BoujeeEnjinia1701/heliolite/cad/drawings/HLT-DWG-001.pdf

CONCEPT, NOT FOR FABRICATION | HelioLite · github.com/BoujeeEnjinia1701/heliolite

FRONT VIEW
Scale 1:25; looking at the front (along +Y)

TOP VIEW
Scale 1:25; looking down (along -Z)

RIGHT VIEW
Scale 1:25; looking at the right side (along -X)

928

934

2,200 axis

2265

1,712 mast top

600 mirror
680 arms c/c

1,100 box base

550

ISOMETRIC VIEW, TRACKING POSE
Not to scale; seen from the front right and above, about 30 deg elevation

MAIN DIMENSIONS AND INTERFACES (MM)
Mirror 600 x 600 x 3 glass on 4 ACP, EPDM edge channel; sweep radius 301 Elevation axis at Z 2,200; 25 sq. torque tube, 14 trunnions
Yoke: 40 x 60 x 2 alu. tube arms at X +/-340; gaps 20 (arm), 56 (crossbar) Drives: NEMA17 on NMRV030-class 50:1, envelope 80 x 97 x 63, 14 bore Mast 60.3 x 3.9 galv. pipe, 1,700 long; floor flange; cap 160 sq. x 8 Anchor flange 220 dia.; ground screw 76 x 800 (not shown)
Anemometer at Z 1,500, reach 550; controller box at Z 1,100
Stow lug 8 thk at X -307; pad and pawl at R 55 on a 6 alu. bracket, -X arm
Preload spring cans 50 dia.: -X trunnion and mast top
Top mass about 12.99 kg, fitted in two lifts; stow face-down in 23 s (HLT-CAL-001) Orthographic views stowed at azimuth 0; front from -Y, right from +X
REV | DESCRIPTION | DATE | BY
P1 | Preliminary GA for TRL 3 (from cad/src/model.py) | 2026-09-25 | AC
P2 | Stow stop and latch, preload springs added (DDR-002) | 2026-09-25 | AC
P3 | Layout and labels tidied | 2026-09-25 | AC
P4 | Design for construction (DDR-003): tube yoke, fixings | 2026-10-01 | AC
P5 | Decisions of 2026-10-02: alu. latch bracket, EPDM edge channel | 2026-10-02 | AC
HELIOLITE | github.com/BoujeeEnjinia1701/heliolite

## General arrangement

DRAWING NO.
HLT-DWG-001

REV
P5

SHEET
1 of 1

SIZE

## ANSI B

SCALE
1:25

UNITS
mm
PROJECTION | DATE
2026-10-02

DRAWN
Amish Chadha

MATERIAL / NOTES
Glass mirror on ACP; aluminum tube yoke; NMRV030-class drives; 60.3 mm galv. pipe. PRELIMINARY, NOT FOR FABRICATION
Licensed CERN-OHL-S-2.0 · Design Molecule Lab · designmolecule.com | Generated from cad/src; do not edit by hand
