BoujeeEnjinia1701/heliolite/cad/drawings/HLT-DWG-104.pdf

### BUILD PLAN SKETCH, PLAN NOT YET BUILT HelioLite · github.com/BoujeeEnjinia1701/heliolite

FRONT VIEW
Scale 1:1; looking at the front (along +Y)

TOP VIEW
Scale 1:1; looking down (along -Z)

RIGHT VIEW
Scale 1:1; looking at the right side (along -X)

8

94 38

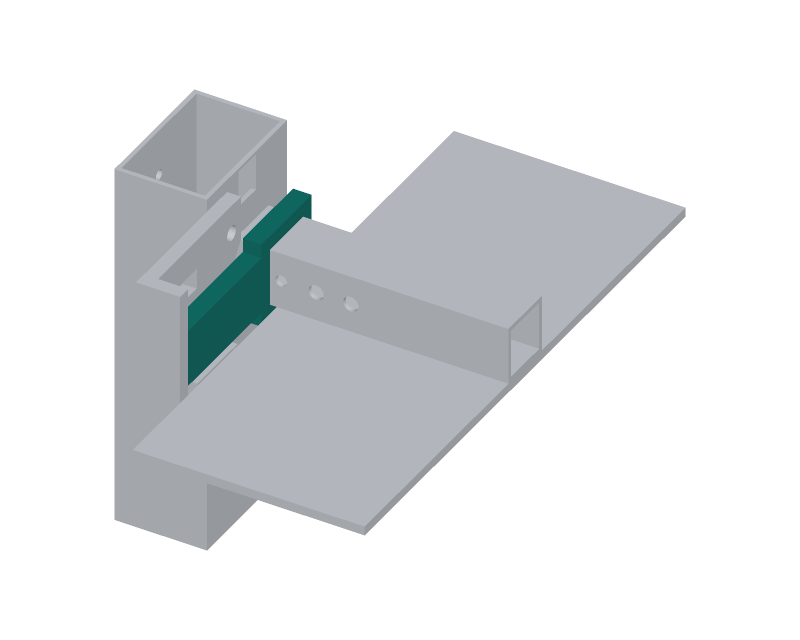
[picture p6: figure]

WHERE IT GOES
This part in colour, its neighbours in grey

HOW TO MAKE IT AND HOW IT FITS
Cut from 8 mm steel plate: a collar 37.5 mm square with a
tongue 25 mm wide running out to 75 mm from the collar's centre. Cut the 25 mm square hole in the collar: drill 20 mm, file square to a sliding fit on the torque tube.
Drill and tap M5 through the collar side opposite the tongue
for a set screw.
On one face of the tongue, 30 mm from the centre: a 6 mm hole 3 mm deep for the homing magnet (glue it in).
Round the tongue corners 2 mm and break all edges.
Fit: slides onto the left end of the torque tube, magnet toward the arm, mid-plane 11 mm from the tube end; set screw into the spot on the tube, medium threadlocker.
When stowed, the tongue rests on the stop pad and the latch pawl closes over it.
Check: the tongue is square to the tube and does not rock.
REV | DESCRIPTION | DATE | BY
P1 | Making sketch for the prototype build plan | 2026-10-02 | AC
HELIOLITE | github.com/BoujeeEnjinia1701/heliolite

## HelioLite stow lug: making sketch

DRAWING NO.
HLT-DWG-104

REV
P1

SHEET
1 of 1

SIZE

## ANSI B

SCALE
1:1

UNITS
mm
PROJECTION | DATE
2026-10-02

DRAWN
Amish Chadha

MATERIAL / NOTES
Steel plate 8 mm, S275 or similar, painted
Licensed CERN-OHL-S-2.0 · Design Molecule Lab · designmolecule.com | Generated from cad/src; do not edit by hand
