BoujeeEnjinia1701/heliolite/cad/drawings/HLT-DWG-107.pdf

### BUILD PLAN SKETCH, PLAN NOT YET BUILT HelioLite · github.com/BoujeeEnjinia1701/heliolite

FRONT VIEW
Scale 1:5; looking at the front (along +Y)

TOP VIEW
Scale 1:5; looking down (along -Z)

RIGHT VIEW
Scale 1:5; looking at the right side (along -X)

40

60 397

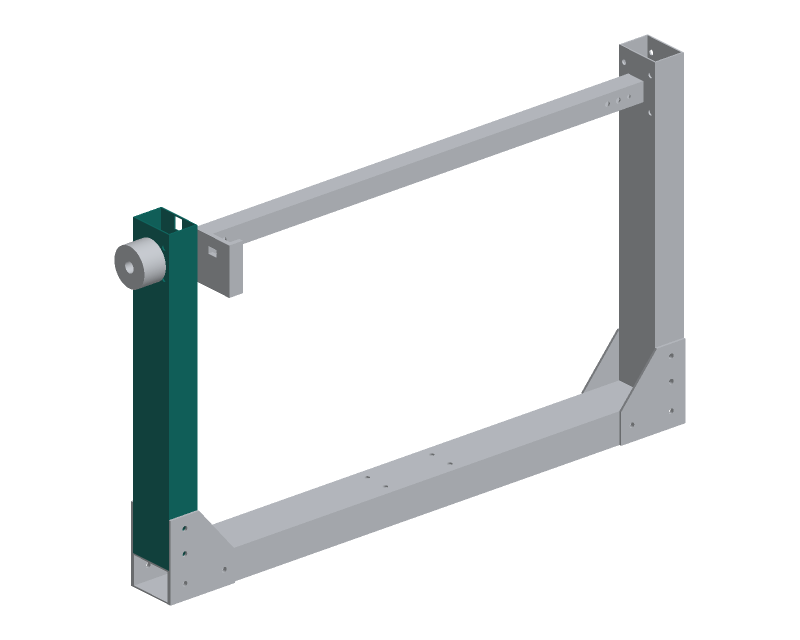
[picture p7: figure]

WHERE IT GOES
This part in colour, its neighbours in grey

HOW TO MAKE IT AND HOW IT FITS
Cut and drill as the right arm (HLT-DWG-106) for length, bush hole and gusset bolt holes, but without the four gearbox holes.
Spring can holes: three 4.5 mm on a 40 mm circle round the bush hole, outer side only.
Latch bracket holes: two 6.5 mm through both sides, 8 mm from the front face, 18 mm and 55 mm below the top end.
Hall switch window: 13 mm wide and 16 mm tall through the inner side only, 1.5 mm below the top end, centred across the side. Fit: as the right arm; the latch bracket bolts to the inner side
at the front, the spring can to the outer side.
Check: lay both arms side by side: bush holes and gusset holes match.
REV | DESCRIPTION | DATE | BY
P1 | Making sketch for the prototype build plan | 2026-10-02 | AC
HELIOLITE | github.com/BoujeeEnjinia1701/heliolite

## HelioLite left arm (latch side): making sketch

DRAWING NO.
HLT-DWG-107

REV
P1

SHEET
1 of 1

SIZE

## ANSI B

SCALE
1:5

UNITS
mm
PROJECTION | DATE
2026-10-02

DRAWN
Amish Chadha

MATERIAL / NOTES
Aluminum rectangular tube 60 x 40 x 2 mm, 6063
Licensed CERN-OHL-S-2.0 · Design Molecule Lab · designmolecule.com | Generated from cad/src; do not edit by hand
