BoujeeEnjinia1701/heliolite/cad/drawings/HLT-DWG-110.pdf

### BUILD PLAN SKETCH, PLAN NOT YET BUILT HelioLite · github.com/BoujeeEnjinia1701/heliolite

FRONT VIEW
Scale 1:1; looking at the front (along +Y)

TOP VIEW
Scale 1:1; looking down (along -Z)

RIGHT VIEW
Scale 1:1; looking at the right side (along -X)

27

68 62

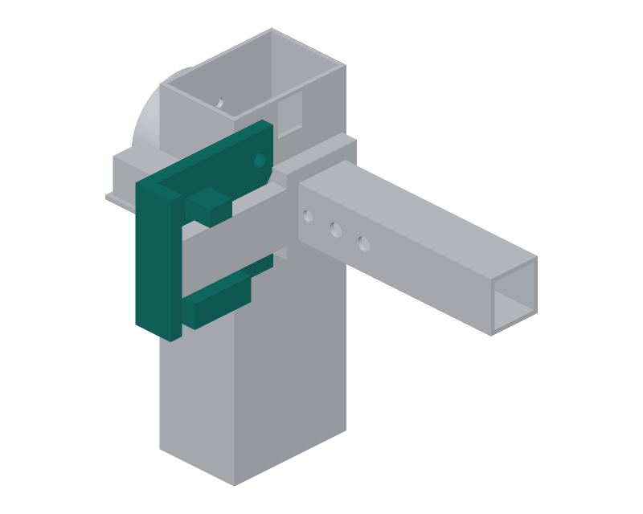
[picture p8: figure]

WHERE IT GOES
This part in colour, its neighbours in grey

HOW TO MAKE IT AND HOW IT FITS
Bracket: cut 62 mm of 6 mm aluminum angle with legs of at least 70 and 20 mm. Trim the long leg to 68 mm and the short leg to 19 mm overall (13 mm clear of the long leg). No bending.
In the long leg: a 21 mm radius bite at the back edge, centred
31 mm up, clear of the turning tube end; a 14 x 9 mm slot for
the pawl, 21 mm from the front edge, 40 mm up. Two 6.6 mm countersunk holes 7 mm from the back edge, 12.5 and 49.5 mm up. Stop block: 13 x 30 x 11.5 mm aluminum bar, screwed to the leg's foot with two M5 screws; bond the 3 mm polyurethane pad on top. Pawl: 26 mm of 12 x 8 mm steel bar; chamfer the top of its tip
45 degrees by 4 mm; tap M3 in the tail for the solenoid plunger. Fit: long leg flat on the left arm's inner side, two M6
countersunk screws; the pawl slides in the slot over the lug. Check: the pawl slides freely 12 mm; pad top 0.5 mm under the stowed lug.
REV | DESCRIPTION | DATE | BY
P1 | Making sketch for the prototype build plan | 2026-10-02 | AC
HELIOLITE | github.com/BoujeeEnjinia1701/heliolite

## HelioLite latch bracket, stop block and pawl: making sketch

DRAWING NO.
HLT-DWG-110

REV
P1

SHEET
1 of 1

SIZE

## ANSI B

SCALE
1:1

UNITS
mm
PROJECTION | DATE
2026-10-02

DRAWN
Amish Chadha

MATERIAL / NOTES
Aluminum angle 6 mm and bar 15 x 30 mm, 6063-T6; steel bar 12 x 8 mm (pawl)
Licensed CERN-OHL-S-2.0 · Design Molecule Lab · designmolecule.com | Generated from cad/src; do not edit by hand
