BoujeeEnjinia1701/heliolite/cad/drawings/HLT-DWG-114.pdf

### BUILD PLAN SKETCH, PLAN NOT YET BUILT HelioLite · github.com/BoujeeEnjinia1701/heliolite

FRONT VIEW
Scale 1:1; looking at the front (along +Y)

TOP VIEW
Scale 1:1; looking down (along -Z)

RIGHT VIEW
Scale 1:1; looking at the right side (along -X)

30

50 50

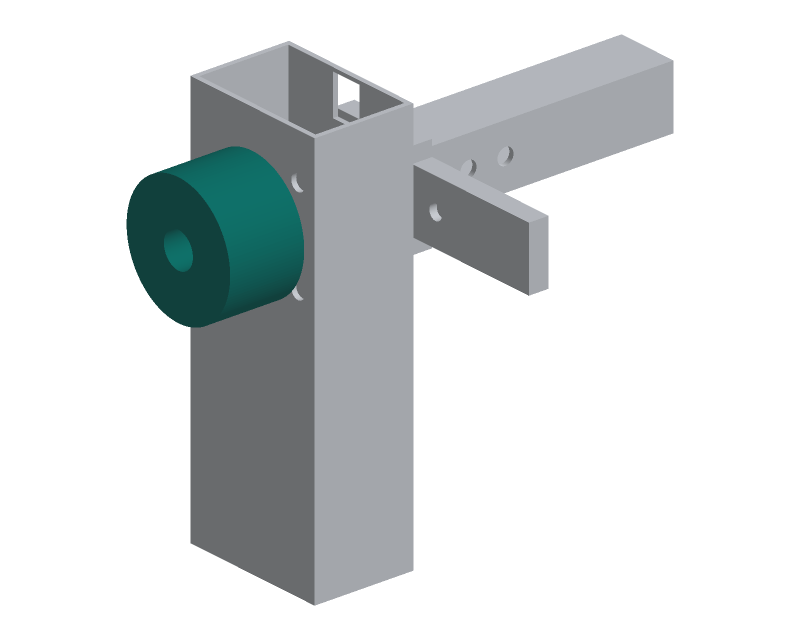
[picture p9: figure]

WHERE IT GOES
This part in colour, its neighbours in grey

HOW TO MAKE IT AND HOW IT FITS
Elevation can: a 50 mm diameter cup 30 mm long with a 14 mm centre hole through its closed end, the open end toward the arm. Three 4.5 mm holes on a 40 mm circle, lengthwise, for M4 screws into the left arm and plug. A 3 mm pin hole near the rim inside holds the spring's outer end.
Azimuth can: the same cup at 52.5 mm diameter, a push fit in the mast pipe, with an M5 insert in its side for a screw through
the pipe wall, 37 mm below the pipe's top end.
Fit the bought flat spiral spring: inner end in the stub's slot
(or the shaft's), outer end on the pin. Wind it 1 turn before fixing so it holds about 3 N m toward stow.
Check: the spring holds the shaft one way with no slack.
REV | DESCRIPTION | DATE | BY
P1 | Making sketch for the prototype build plan | 2026-10-02 | AC
HELIOLITE | github.com/BoujeeEnjinia1701/heliolite

## HelioLite spring can (make 2, printed): making sketch

DRAWING NO.
HLT-DWG-114

REV
P1

SHEET
1 of 1

SIZE

## ANSI B

SCALE
1:1

UNITS
mm
PROJECTION | DATE
2026-10-02

DRAWN
Amish Chadha

MATERIAL / NOTES
ASA, printed; 100 % infill
Licensed CERN-OHL-S-2.0 · Design Molecule Lab · designmolecule.com | Generated from cad/src; do not edit by hand
