BoujeeEnjinia1701/heliolite/cad/drawings/HLT-DWG-101.pdf

### BUILD PLAN SKETCH, PLAN NOT YET BUILT HelioLite · github.com/BoujeeEnjinia1701/heliolite

FRONT VIEW
Scale 1:5; looking at the front (along +Y)

TOP VIEW
Scale 1:5; looking down (along -Z)

RIGHT VIEW
Scale 1:5; looking at the right side (along -X)

25

560 40

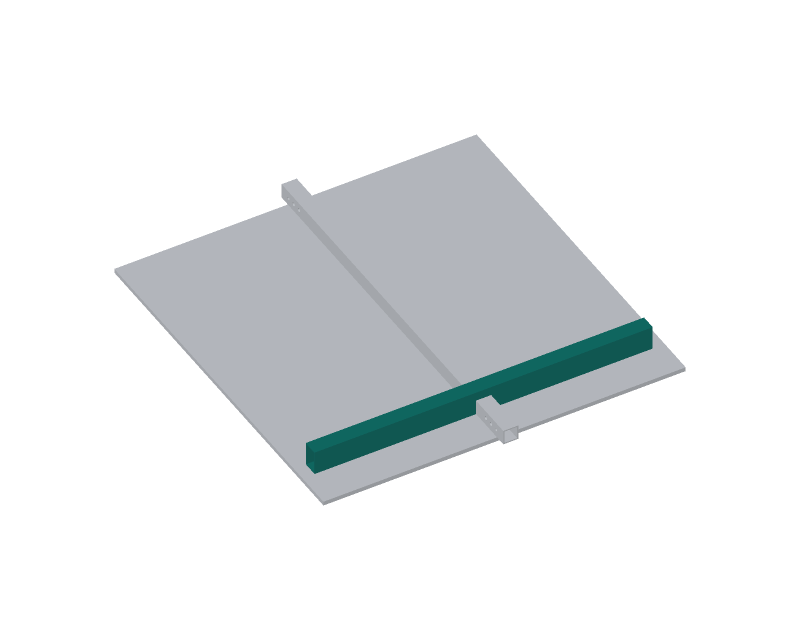
[picture p52: figure]

WHERE IT GOES
This part in colour, its neighbours in grey

HOW TO MAKE IT AND HOW IT FITS
Cut two 560 mm lengths of 25 x 40 x 1.5 mm tube; square and deburr. Tunnel for the torque tube, at mid-length (280 mm from each end):
a notch 25.5 mm long and 25.25 mm deep, cut from one 25 mm face (the face that goes on the panel) down through both 40 mm sides. Saw the two sides, chain drill and file the floor flat.
Push a 25 mm tube offcut through the tunnel: it must slide, not rock. Fit plastic end caps in both ends.
Fit: the notched face is bonded to the back of the backing panel with structural silicone, the rib centre line 227.5 mm from the panel centre line and its ends 20 mm in from the panel edges.
The torque tube runs through both tunnels and touches the panel. Check: both tunnels line up when the ribs lie side by side.
REV | DESCRIPTION | DATE | BY
P1 | Making sketch for the prototype build plan | 2026-10-01 | AC
HELIOLITE | github.com/BoujeeEnjinia1701/heliolite

## HelioLite rib tube (make 2): making sketch

DRAWING NO.
HLT-DWG-101

REV
P1

SHEET
1 of 1

SIZE

## ANSI B

SCALE
1:5

UNITS
mm
PROJECTION | DATE
2026-10-01

DRAWN
Amish Chadha

MATERIAL / NOTES
Aluminum rectangular tube 25 x 40 x 1.5 mm, 6063
Licensed CERN-OHL-S-2.0 · Design Molecule Lab · designmolecule.com | Generated from cad/src; do not edit by hand
