BoujeeEnjinia1701/heliolite/cad/drawings/HLT-DWG-102.pdf

### BUILD PLAN SKETCH, PLAN NOT YET BUILT HelioLite · github.com/BoujeeEnjinia1701/heliolite

FRONT VIEW
Scale 1:5; looking at the front (along +Y)

TOP VIEW
Scale 1:5; looking down (along -Z)

RIGHT VIEW
Scale 1:5; looking at the right side (along -X)

636

25 25

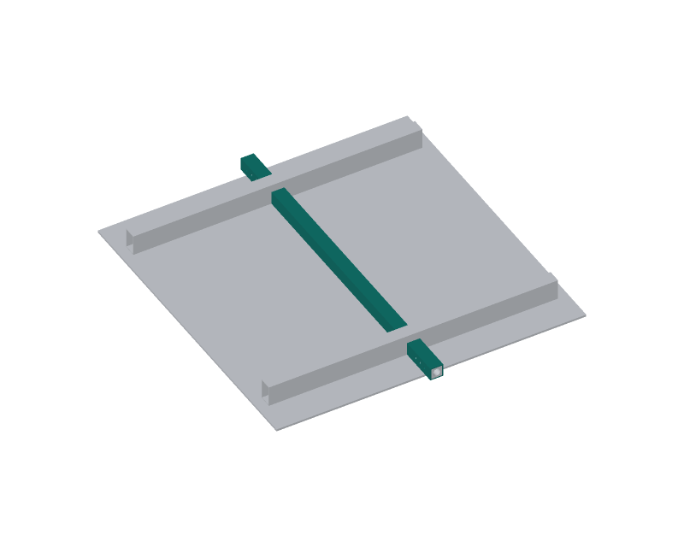
[picture p53: figure]

WHERE IT GOES
This part in colour, its neighbours in grey

HOW TO MAKE IT AND HOW IT FITS
Cut to 635 mm (1 mm shorter than the 636 mm between the bush flanges, so the mirror drops into the yoke). Square both ends.
Through both side walls, 6.5 mm holes 35 and 50 mm from each end (end block bolts), on the centre line of the side.
Through both side walls, a 5 mm hole 20 mm from each end (cross pin): drill these with the end blocks and stubs in place (step 11).
On the left end only: a shallow 4 mm spot 11 mm from the end on
the face away from the panel, for the stow lug's set screw.
Deburr inside and out so the end blocks slide in.
Fit: runs through both rib tunnels, its top face bonded to the panel with structural silicone; ends 318 mm each side of the centre. Check: straight within 0.5 mm over its length on a flat bench.
REV | DESCRIPTION | DATE | BY
P1 | Making sketch for the prototype build plan | 2026-10-01 | AC
HELIOLITE | github.com/BoujeeEnjinia1701/heliolite

## HelioLite torque tube: making sketch

DRAWING NO.
HLT-DWG-102

REV
P1

SHEET
1 of 1

SIZE

## ANSI B

SCALE
1:5

UNITS
mm
PROJECTION | DATE
2026-10-01

DRAWN
Amish Chadha

MATERIAL / NOTES
Aluminum square tube 25 x 25 x 2 mm, 6063
Licensed CERN-OHL-S-2.0 · Design Molecule Lab · designmolecule.com | Generated from cad/src; do not edit by hand
