BoujeeEnjinia1701/heliolite/cad/drawings/HLT-DWG-103.pdf

### BUILD PLAN SKETCH, PLAN NOT YET BUILT HelioLite · github.com/BoujeeEnjinia1701/heliolite

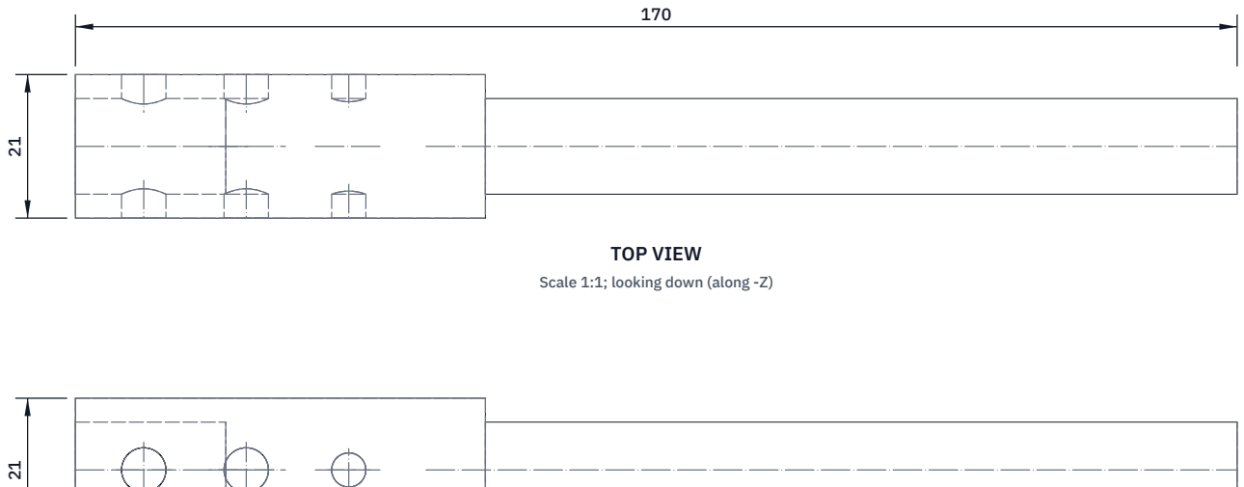
[picture p54: figure]
TOP VIEW; Scale 1:1; looking down (along -Z)

FRONT VIEW
Scale 1:1; looking at the front (along +Y)

RIGHT VIEW
Scale 1:1; looking at the right side (along -X)

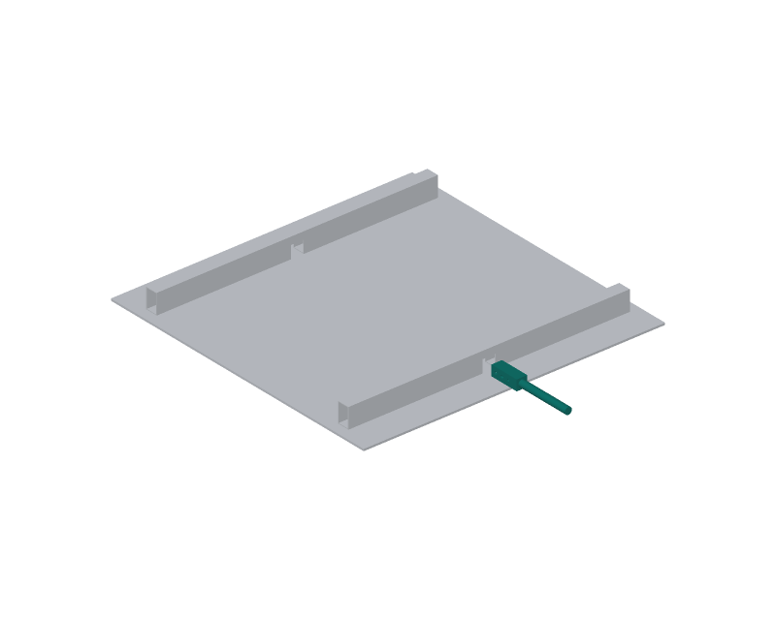
[picture p55: figure]

WHERE IT GOES
This part in colour, its neighbours in grey

HOW TO MAKE IT AND HOW IT FITS
End blocks (make 2): cut 60 mm of 22 mm square bar; file to 21 mm square, a sliding fit in the tube. Drill and ream 14 mm along
the centre, right through. Cross holes 6.5 mm at 10 and 25 mm from the inner end, through two opposite faces.
Stubs: cut 14 mm keyed shaft (5 mm key) to 148 mm for the drive (right) side and 108 mm for the spring (left) side.
Each stub goes 38 mm into its block. With the stub in the block in the tube, drill 5 mm through tube, block and stub 20 mm from the tube end and drive in a 5 x 24 mm roll pin (step 11).
Left stub only: saw a 3 mm slot 10 mm deep across its outer end for the inner end of the spiral spring.
Fit: block bolted in the tube end with two M6 bolts; stub through the bronze bush, into the gearbox bore (right) or spring can (left). Check: the stub turns the tube with no play once pinned.
REV | DESCRIPTION | DATE | BY
P1 | Making sketch for the prototype build plan | 2026-10-01 | AC
HELIOLITE | github.com/BoujeeEnjinia1701/heliolite

## HelioLite trunnion end block and stub: making sketch

DRAWING NO.
HLT-DWG-103

REV
P1

SHEET
1 of 1

SIZE

## ANSI B

SCALE
1:1

UNITS
mm
PROJECTION | DATE
2026-10-01

DRAWN
Amish Chadha

MATERIAL / NOTES
Aluminum square bar 22 mm (block); 14 mm keyed steel shaft (stub)
Licensed CERN-OHL-S-2.0 · Design Molecule Lab · designmolecule.com | Generated from cad/src; do not edit by hand
