BoujeeEnjinia1701/heliolite/cad/drawings/HLT-DWG-105.pdf

### BUILD PLAN SKETCH, PLAN NOT YET BUILT HelioLite · github.com/BoujeeEnjinia1701/heliolite

FRONT VIEW
Scale 1:5; looking at the front (along +Y)

TOP VIEW
Scale 1:5; looking down (along -Z)

RIGHT VIEW
Scale 1:5; looking at the right side (along -X)

720

60 40

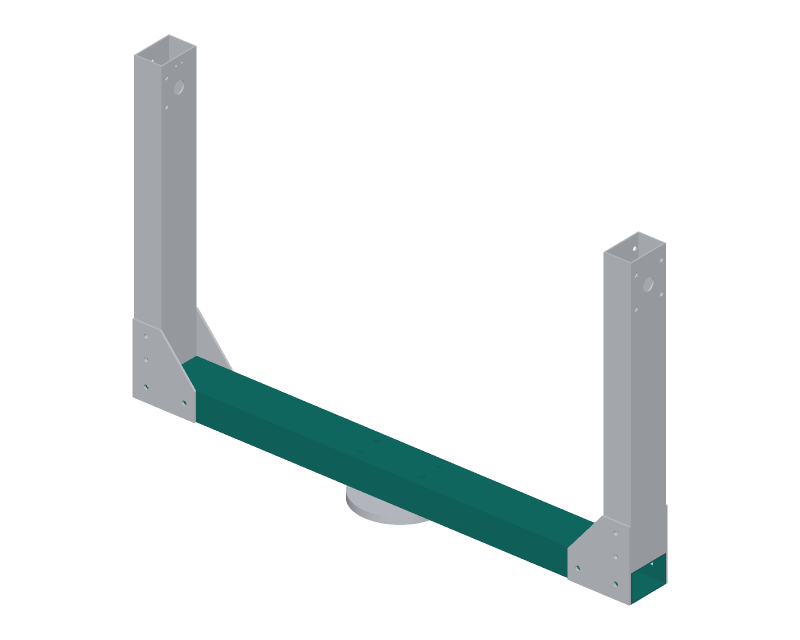
[picture p56: figure]

WHERE IT GOES
This part in colour, its neighbours in grey

HOW TO MAKE IT AND HOW IT FITS
Cut 720 mm of 60 x 40 x 2 mm tube; square and deburr the ends. Lay it with a 60 mm face up. All holes 6.5 mm.
Gusset bolt holes, horizontal through both 40 mm sides, at mid-height: 20 mm and 75 mm in from each end.
Turntable bolt holes, vertical through top and bottom: four holes, 45 mm each side of the centre and 15 mm each side of the centre line.
Slide a 6 mm bore aluminum crush sleeve into each bolt hole pair (cut to the inside height) so bolts do not crush the tube.
Fit: sits flat on the turntable disc, held by four M6 bolts into
the disc's tapped holes; the arms stand on its ends.
Check: holes in line; the tube lies flat on the disc.
REV | DESCRIPTION | DATE | BY
P1 | Making sketch for the prototype build plan | 2026-10-01 | AC
HELIOLITE | github.com/BoujeeEnjinia1701/heliolite

## HelioLite crossbar: making sketch

DRAWING NO.
HLT-DWG-105

REV
P1

SHEET
1 of 1

SIZE

## ANSI B

SCALE
1:5

UNITS
mm
PROJECTION | DATE
2026-10-01

DRAWN
Amish Chadha

MATERIAL / NOTES
Aluminum rectangular tube 60 x 40 x 2 mm, 6063
Licensed CERN-OHL-S-2.0 · Design Molecule Lab · designmolecule.com | Generated from cad/src; do not edit by hand
