BoujeeEnjinia1701/heliolite/cad/drawings/HLT-DWG-106.pdf

### BUILD PLAN SKETCH, PLAN NOT YET BUILT HelioLite · github.com/BoujeeEnjinia1701/heliolite

FRONT VIEW
Scale 1:5; looking at the front (along +Y)

TOP VIEW
Scale 1:5; looking down (along -Z)

RIGHT VIEW
Scale 1:5; looking at the right side (along -X)

40

60 397

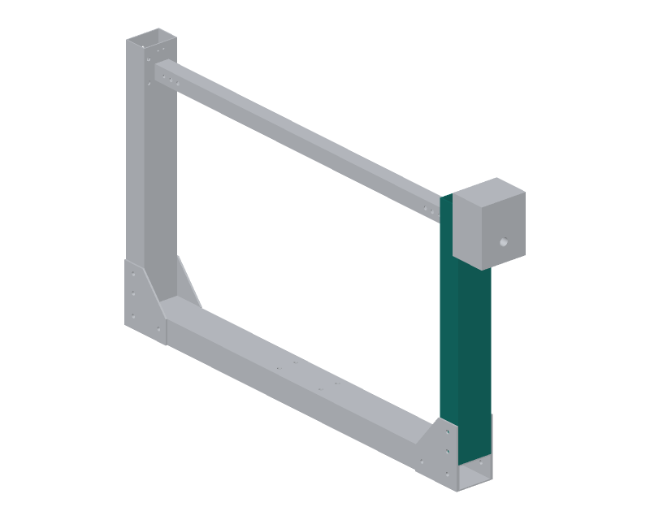
[picture p57: figure]

WHERE IT GOES
This part in colour, its neighbours in grey

HOW TO MAKE IT AND HOW IT FITS
Cut 397 mm of 60 x 40 x 2 mm tube; square and deburr. The 60 mm faces are the sides; the 40 mm faces are the front and back.
Bush hole: 18 mm through both sides, centred, 40 mm below the top end. Drill 6 mm pilot, open with a step drill, ream.
Gearbox holes (right arm): four 6.5 mm through both sides on a 44 mm square round the bush hole (22 mm each way). Check the gearbox's output-face holes before drilling.
Gusset bolt holes: 6.5 mm through the front and back faces, centred, 15 mm and 45 mm above the bottom end.
Fit: stands on the crossbar end; two gussets clamp it; the bearing plug fills its top 75 mm; the gearbox bolts to the
outer side.
Check: the bush hole is square to the side (a 14 mm rod through it stands at 90 degrees to the arm).
REV | DESCRIPTION | DATE | BY
P1 | Making sketch for the prototype build plan | 2026-10-01 | AC
HELIOLITE | github.com/BoujeeEnjinia1701/heliolite

## HelioLite right arm (drive side): making sketch

DRAWING NO.
HLT-DWG-106

REV
P1

SHEET
1 of 1

SIZE

## ANSI B

SCALE
1:5

UNITS
mm
PROJECTION | DATE
2026-10-01

DRAWN
Amish Chadha

MATERIAL / NOTES
Aluminum rectangular tube 60 x 40 x 2 mm, 6063
Licensed CERN-OHL-S-2.0 · Design Molecule Lab · designmolecule.com | Generated from cad/src; do not edit by hand
