BoujeeEnjinia1701/heliolite/cad/drawings/HLT-DWG-108.pdf

### BUILD PLAN SKETCH, PLAN NOT YET BUILT HelioLite · github.com/BoujeeEnjinia1701/heliolite

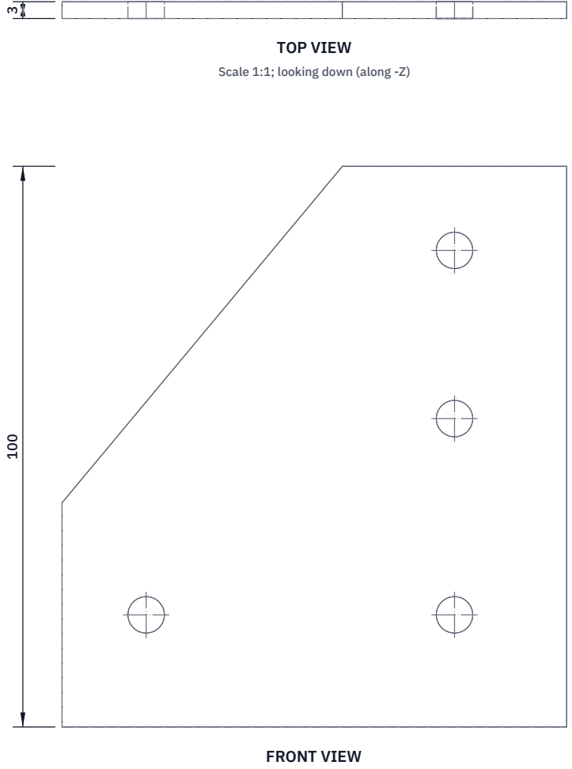
[picture p58: figure]
FRONT VIEW; TOP VIEW; Scale 1:1; looking down (along -Z)

Scale 1:1; looking at the front (along +Y)

RIGHT VIEW
Scale 1:1; looking at the right side (along -X)

90

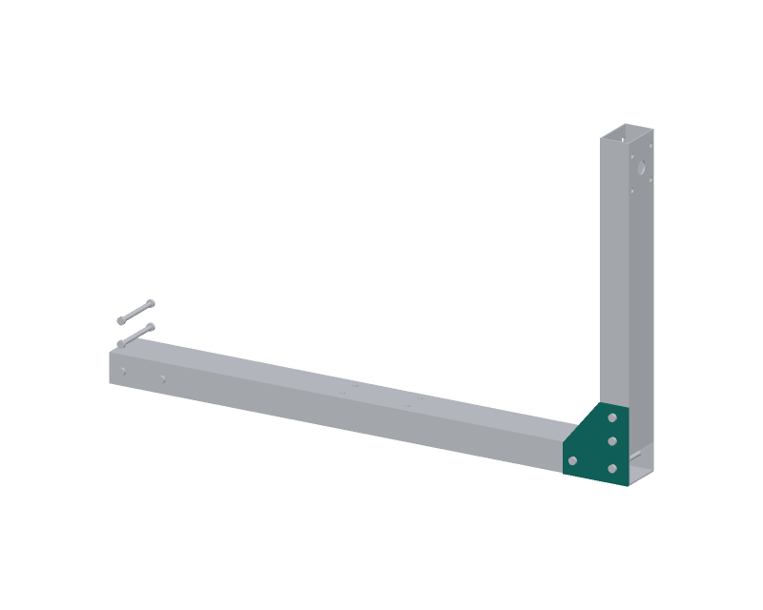
[picture p59: figure]

WHERE IT GOES
This part in colour, its neighbours in grey

HOW TO MAKE IT AND HOW IT FITS
Mark on 3 mm sheet: bottom edge 90 mm, outer edge 100 mm tall, top edge 40 mm, then a straight edge down to a point 40 mm up the inner end. Cut with a jigsaw or snips; file the edges.
Four 6.5 mm holes, measured from the outer edge and up from the bottom edge: 20 and 20; 75 and 20; 20 and 55; 20 and 85.
All four plates are the same: drill them as a stack.
Fit: one plate on the front and one on the back of each arm
foot, bottom edge flush with the crossbar's bottom face and outer edge flush with its end. Four M6 bolts go through plate, tube and plate, with crush sleeves and nyloc nuts.
Check: the arm stands square to the crossbar when bolted.
REV | DESCRIPTION | DATE | BY
P1 | Making sketch for the prototype build plan | 2026-10-01 | AC
HELIOLITE | github.com/BoujeeEnjinia1701/heliolite

## HelioLite gusset plate (make 4): making sketch

DRAWING NO.
HLT-DWG-108

REV
P1

SHEET
1 of 1

SIZE

## ANSI B

SCALE
1:1

UNITS
mm
PROJECTION | DATE
2026-10-01

DRAWN
Amish Chadha

MATERIAL / NOTES
Aluminum sheet 3 mm, 5052 or 6061
Licensed CERN-OHL-S-2.0 · Design Molecule Lab · designmolecule.com | Generated from cad/src; do not edit by hand
