BoujeeEnjinia1701/heliolite/cad/drawings/HLT-DWG-109.pdf

### BUILD PLAN SKETCH, PLAN NOT YET BUILT HelioLite · github.com/BoujeeEnjinia1701/heliolite

FRONT VIEW
Scale 1:1; looking at the front (along +Y)

TOP VIEW
Scale 1:1; looking down (along -Z)

RIGHT VIEW
Scale 1:1; looking at the right side (along -X)

36

56 75

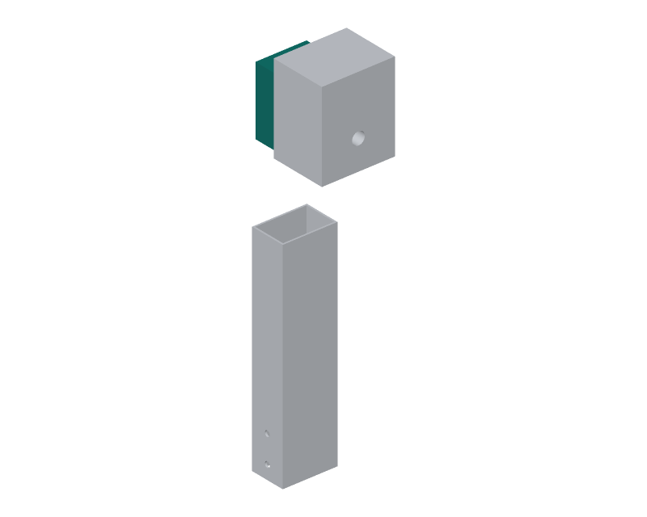
[picture p60: figure]

WHERE IT GOES
This part in colour, its neighbours in grey

HOW TO MAKE IT AND HOW IT FITS
Print a block 36 x 56 x 75 mm with an 18 mm hole across its 36 mm thickness, centred, 40 mm below the top face. Print it standing on its 36 x 56 end so the hole axis is horizontal; six walls so screws bite in solid plastic.
Fit: pressed into the top of each arm, top faces flush; the bronze bush passes through arm side, plug and arm side. Drill the bolt holes (gearbox, latch, spring can) through the plug from the arm's holes once it is in place.
The plug spreads the bolt loads and keeps the thin tube walls from crushing.
Check: a firm press fit; the hole lines up with the arm's 18 mm holes so the bush slides through.
REV | DESCRIPTION | DATE | BY
P1 | Making sketch for the prototype build plan | 2026-10-01 | AC
HELIOLITE | github.com/BoujeeEnjinia1701/heliolite

## HelioLite bearing plug (make 2, printed): making sketch

DRAWING NO.
HLT-DWG-109

REV
P1

SHEET
1 of 1

SIZE

## ANSI B

SCALE
1:1

UNITS
mm
PROJECTION | DATE
2026-10-01

DRAWN
Amish Chadha

MATERIAL / NOTES
ASA, printed; 6 walls, 60 % infill
Licensed CERN-OHL-S-2.0 · Design Molecule Lab · designmolecule.com | Generated from cad/src; do not edit by hand
