BoujeeEnjinia1701/heliolite/cad/drawings/HLT-DWG-111.pdf

### BUILD PLAN SKETCH, PLAN NOT YET BUILT HelioLite · github.com/BoujeeEnjinia1701/heliolite

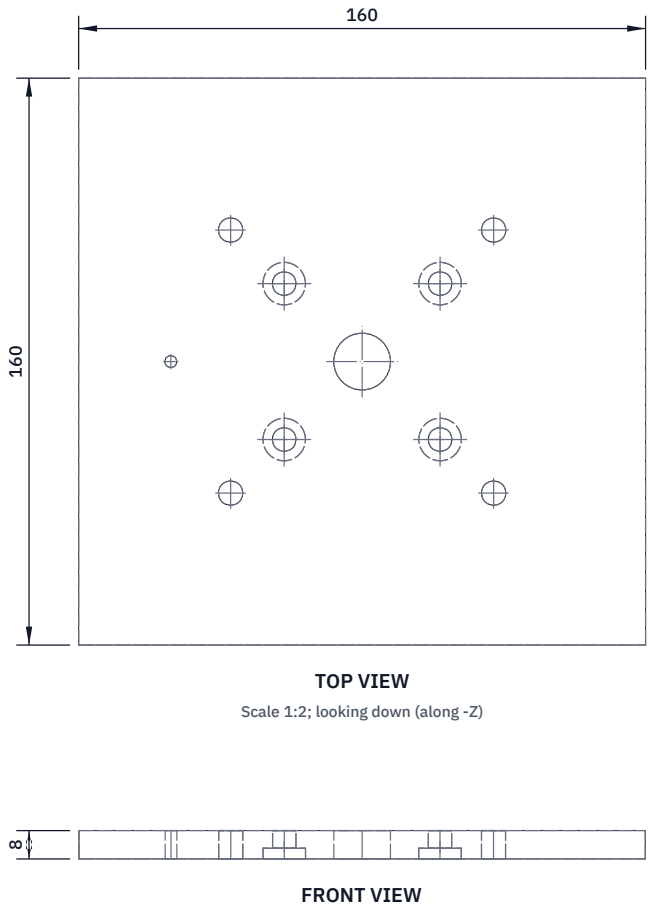
[picture p61: figure]
FRONT VIEW; TOP VIEW; Scale 1:2; looking down (along -Z)

Scale 1:2; looking at the front (along +Y)

RIGHT VIEW
Scale 1:2; looking at the right side (along -X)

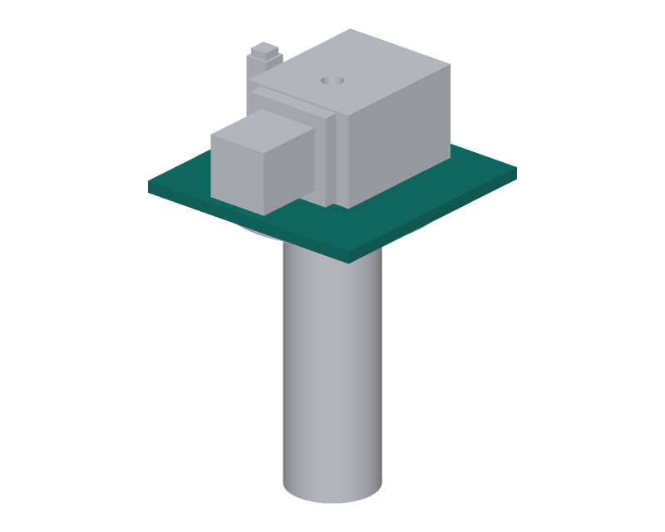
[picture p62: figure]

WHERE IT GOES
This part in colour, its neighbours in grey

HOW TO MAKE IT AND HOW IT FITS
Cut 160 x 160 mm from 8 mm plate; break the edges.
Centre hole 16 mm for the azimuth shaft.
Flange screws: four holes drilled 6.8 mm and tapped M8 on a
105 mm circle at 45 degrees (37.1 mm each way from the centre). Check against your floor flange's holes before drilling.
Gearbox screws: four 6.6 mm holes on a 44 mm square (22 mm each way), countersunk from the underside so the heads sit flush.
Hall post screw: one M4 tapped hole 54 mm from the centre, on the line through the centre square to the motor (top view).
Fit: the gearbox sits on the top face (screws first, from below); the plate then sits on the floor flange, held by four M8 screws up through the flange into the tapped holes.
Check: the shaft passes the centre hole without touching.
REV | DESCRIPTION | DATE | BY
P1 | Making sketch for the prototype build plan | 2026-10-01 | AC
HELIOLITE | github.com/BoujeeEnjinia1701/heliolite

## HelioLite mast cap plate: making sketch

DRAWING NO.
HLT-DWG-111

REV
P1

SHEET
1 of 1

SIZE

## ANSI B

SCALE
1:2

UNITS
mm
PROJECTION | DATE
2026-10-01

DRAWN
Amish Chadha

MATERIAL / NOTES
Steel plate 8 mm, S275, zinc sprayed or painted
Licensed CERN-OHL-S-2.0 · Design Molecule Lab · designmolecule.com | Generated from cad/src; do not edit by hand
