BoujeeEnjinia1701/heliolite/cad/drawings/HLT-DWG-112.pdf

### BUILD PLAN SKETCH, PLAN NOT YET BUILT HelioLite · github.com/BoujeeEnjinia1701/heliolite

FRONT VIEW
Scale 1:2; looking at the front (along +Y)

TOP VIEW
Scale 1:2; looking down (along -Z)

RIGHT VIEW
Scale 1:2; looking at the right side (along -X)

120

120 10

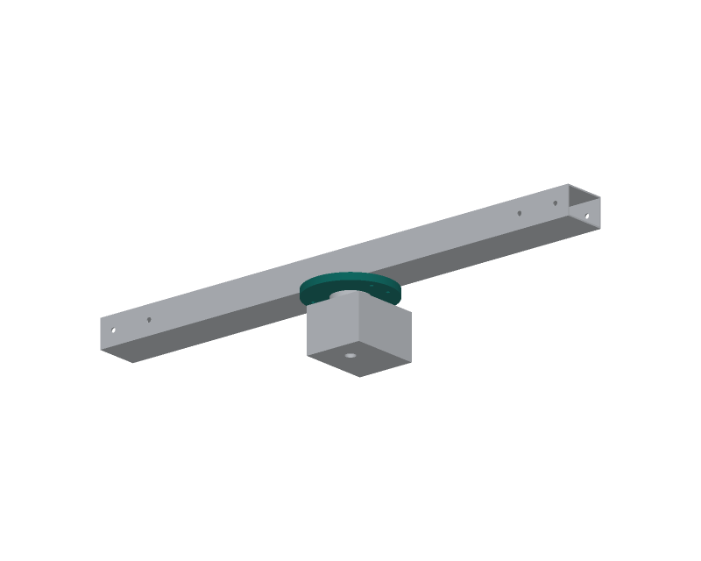
[picture p63: figure]

WHERE IT GOES
This part in colour, its neighbours in grey

HOW TO MAKE IT AND HOW IT FITS
Cut a 120 mm disc from 10 mm plate (or buy a blank); face both sides flat.
Centre hole 30 mm, a close fit on the hub's boss.
Hub screws: four 5.5 mm holes on a 40 mm circle at 45 degrees, countersunk from the top so the crossbar sits flat over them. Crossbar bolts: four holes drilled 5 mm and tapped M6, 45 mm each side of the centre and 15 mm each side of the centre line. Homing magnet: a 6 mm hole 3 mm deep in the underside, 54 mm from the centre on the crossbar's centre line (glue it in).
Fit: the hub screws to its underside; the crossbar bolts to its
top; the whole turns on the azimuth shaft.
Check: the disc runs flat within 0.3 mm at its rim when turned on the shaft.
REV | DESCRIPTION | DATE | BY
P1 | Making sketch for the prototype build plan | 2026-10-01 | AC
HELIOLITE | github.com/BoujeeEnjinia1701/heliolite

## HelioLite turntable disc: making sketch

DRAWING NO.
HLT-DWG-112

REV
P1

SHEET
1 of 1

SIZE

## ANSI B

SCALE
1:2

UNITS
mm
PROJECTION | DATE
2026-10-01

DRAWN
Amish Chadha

MATERIAL / NOTES
Aluminum plate 10 mm, 6082
Licensed CERN-OHL-S-2.0 · Design Molecule Lab · designmolecule.com | Generated from cad/src; do not edit by hand
