BoujeeEnjinia1701/heliolite/cad/drawings/HLT-DWG-113.pdf

### BUILD PLAN SKETCH, PLAN NOT YET BUILT HelioLite · github.com/BoujeeEnjinia1701/heliolite

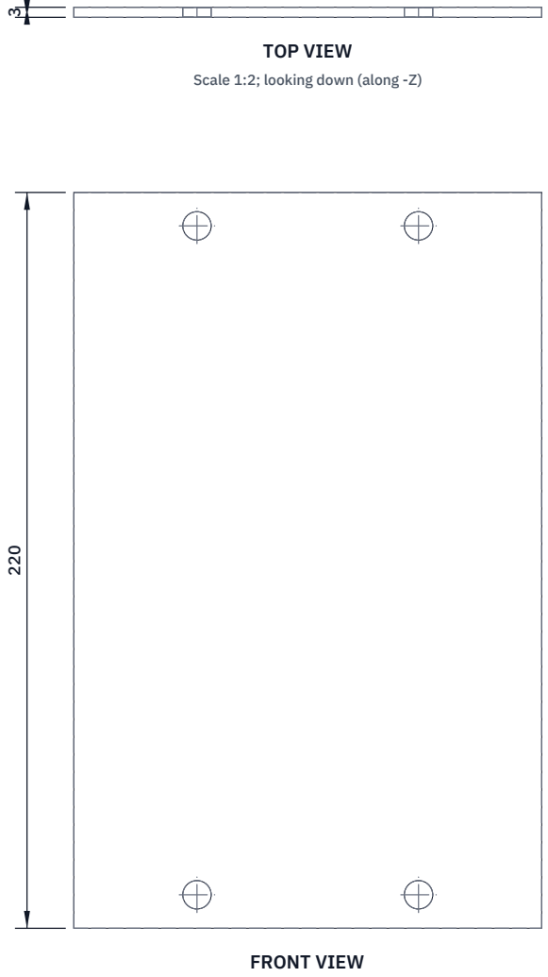
[picture p64: figure]
FRONT VIEW; TOP VIEW; Scale 1:2; looking down (along -Z)

Scale 1:2; looking at the front (along +Y)

RIGHT VIEW
Scale 1:2; looking at the right side (along -X)

140

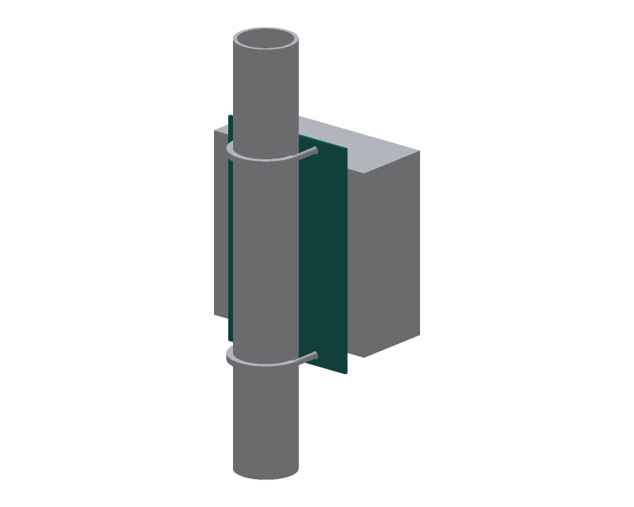
[picture p65: figure]

WHERE IT GOES
This part in colour, its neighbours in grey

HOW TO MAKE IT AND HOW IT FITS
Cut 140 x 220 mm from 3 mm sheet; round the corners 5 mm. U-bolt holes: two pairs of 8.5 mm holes, 66 mm apart, centred across the plate, 10 mm in from the top and bottom edges. Box holes: hold the controller box centred on the plate and drill through its mounting lugs (four 4.5 mm holes).
Fit: the plate's back touches the mast; two 2 in U-bolts go
round the mast and through the plate with nyloc nuts; the box screws to the plate's front with M4 screws.
The box sits 3 mm off the mast, its base 1.1 m above the ground. Check: the plate does not turn on the mast with the nuts tight.
REV | DESCRIPTION | DATE | BY
P1 | Making sketch for the prototype build plan | 2026-10-01 | AC
HELIOLITE | github.com/BoujeeEnjinia1701/heliolite

## HelioLite controller mounting plate: making sketch

DRAWING NO.
HLT-DWG-113

REV
P1

SHEET
1 of 1

SIZE

## ANSI B

SCALE
1:2

UNITS
mm
PROJECTION | DATE
2026-10-01

DRAWN
Amish Chadha

MATERIAL / NOTES
Aluminum sheet 3 mm, 5052
Licensed CERN-OHL-S-2.0 · Design Molecule Lab · designmolecule.com | Generated from cad/src; do not edit by hand
