BoujeeEnjinia1701/heliolite/cad/drawings/HLT-DWG-115.pdf

### BUILD PLAN SKETCH, PLAN NOT YET BUILT HelioLite · github.com/BoujeeEnjinia1701/heliolite

FRONT VIEW
Scale 1:1; looking at the front (along +Y)

TOP VIEW
Scale 1:1; looking down (along -Z)

RIGHT VIEW
Scale 1:1; looking at the right side (along -X)

16

16 69

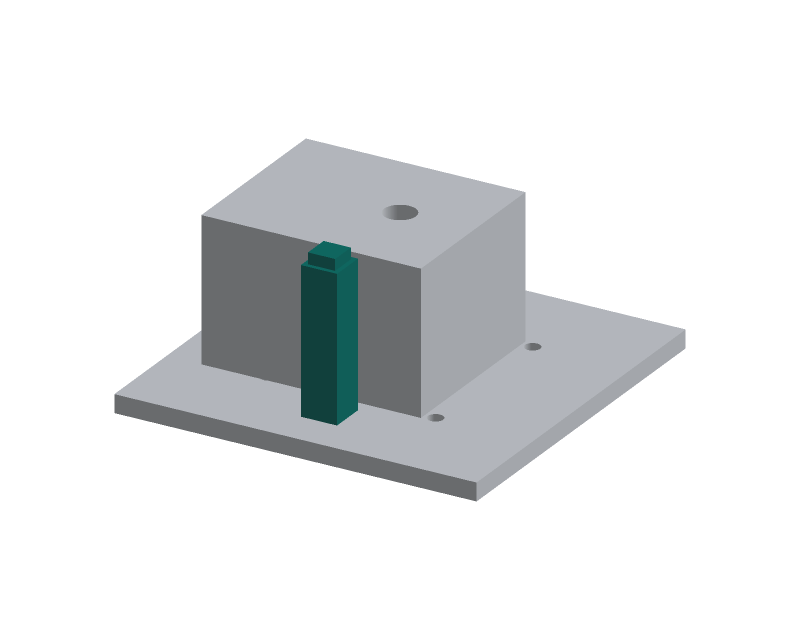
[picture p66: figure]

WHERE IT GOES
This part in colour, its neighbours in grey

HOW TO MAKE IT AND HOW IT FITS
Print a post 16 x 16 mm and 64 mm tall with a 4.5 mm hole down its centre, counterbored 8 mm from the top for the screw head. Fit: one M4 screw down through the post into the tapped hole in the cap plate, 54 mm from the shaft centre.
Glue the Hall switch (12 x 12 x 5 mm) on top, sensing face up. Its face sits 4 mm under the turntable disc, under the magnet when the yoke points at azimuth zero.
Run its lead down the post with the motor lead.
Check: turn the disc by hand: the switch changes state as the magnet passes, and nothing rubs.
REV | DESCRIPTION | DATE | BY
P1 | Making sketch for the prototype build plan | 2026-10-01 | AC
HELIOLITE | github.com/BoujeeEnjinia1701/heliolite

## HelioLite azimuth Hall switch post (printed): making sketch

DRAWING NO.
HLT-DWG-115

REV
P1

SHEET
1 of 1

SIZE

## ANSI B

SCALE
1:1

UNITS
mm
PROJECTION | DATE
2026-10-01

DRAWN
Amish Chadha

MATERIAL / NOTES
ASA, printed; 100 % infill
Licensed CERN-OHL-S-2.0 · Design Molecule Lab · designmolecule.com | Generated from cad/src; do not edit by hand
