BoujeeEnjinia1701/heliolite/cad/drawings/HLT-DWG-001.png

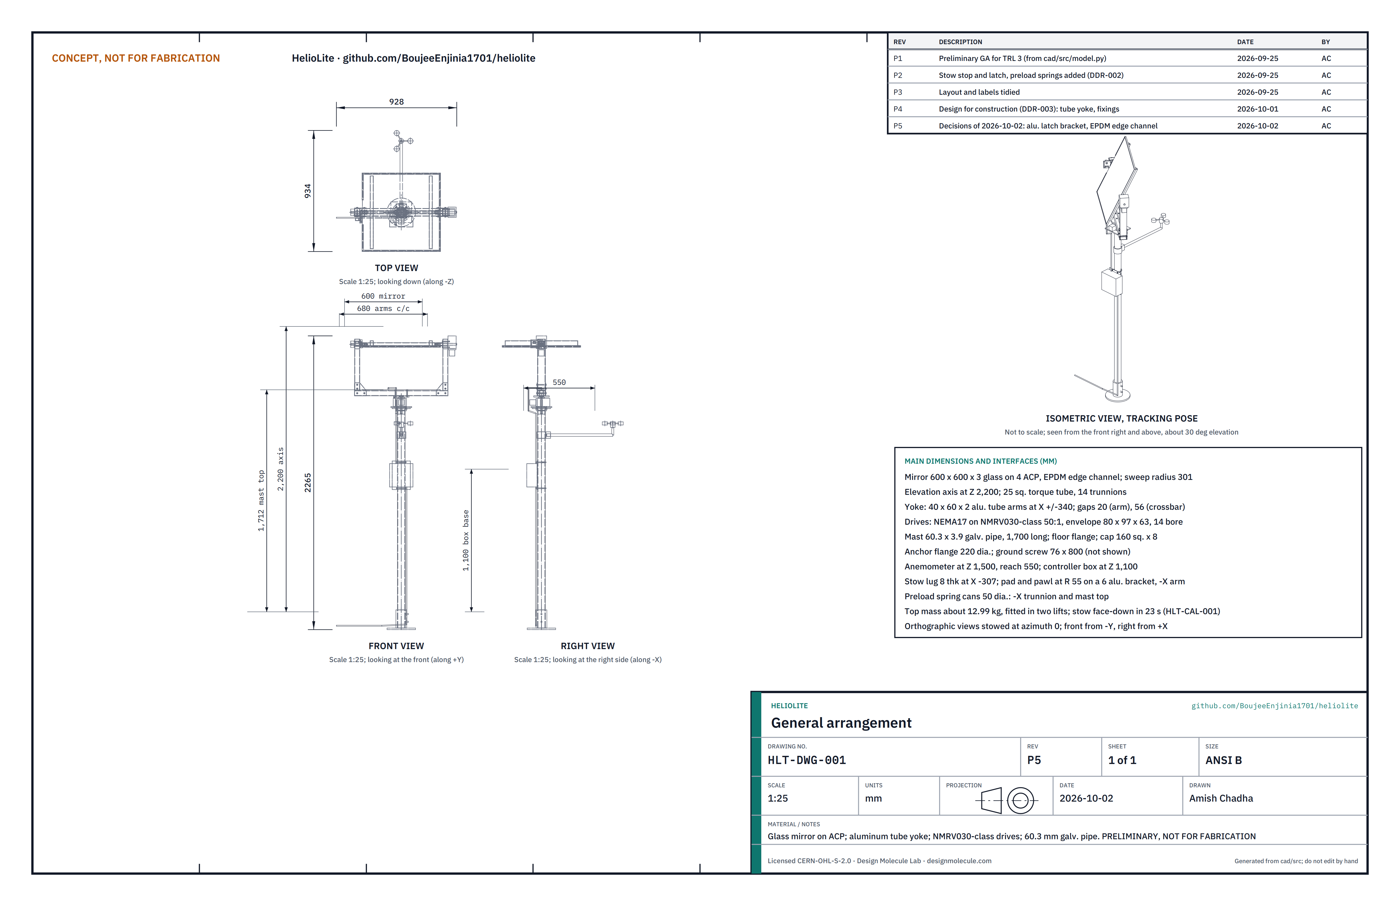
cad/drawings/HLT-DWG-001.png
