BoujeeEnjinia1701/heliolite/media/card.png

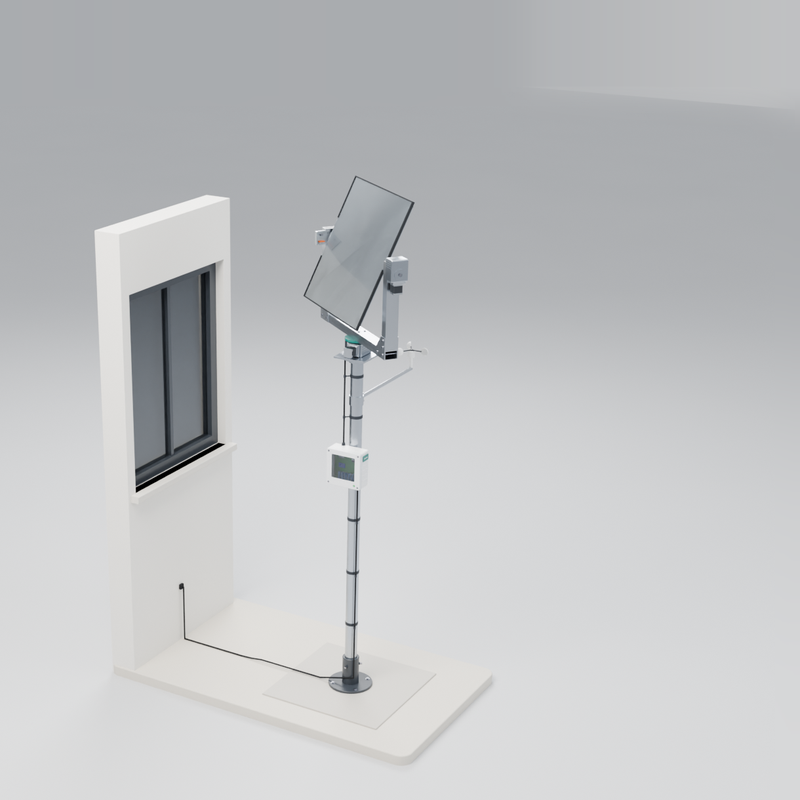
media/card.png
