BoujeeEnjinia1701/heliolite/media/render-detail.png

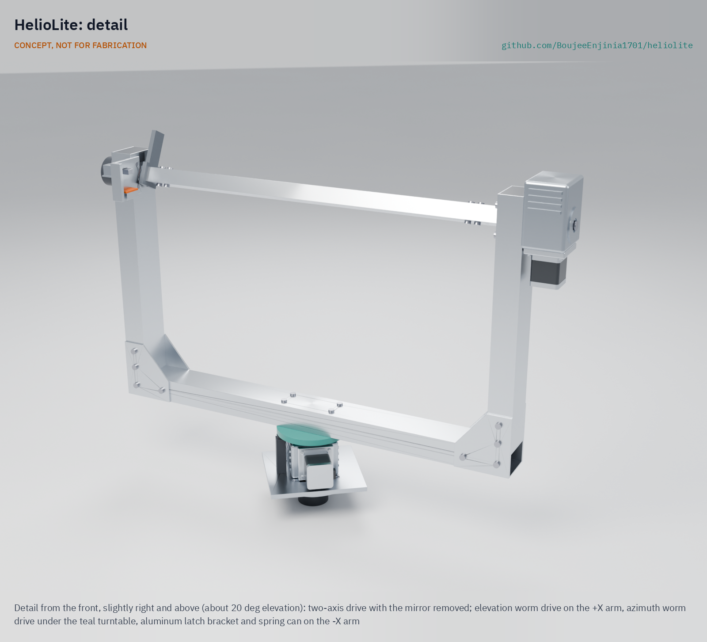
media/render-detail.png
