BoujeeEnjinia1701/heliolite/media/render-exploded.png

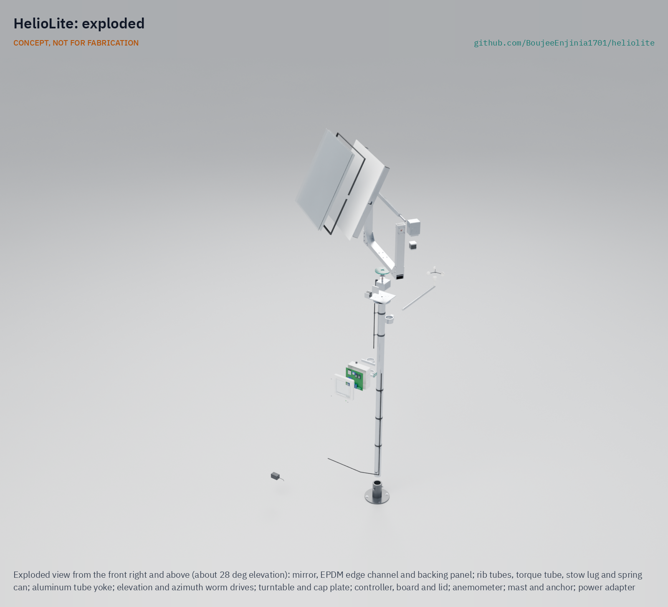
media/render-exploded.png
