BoujeeEnjinia1701/heliolite/media/social-preview.png

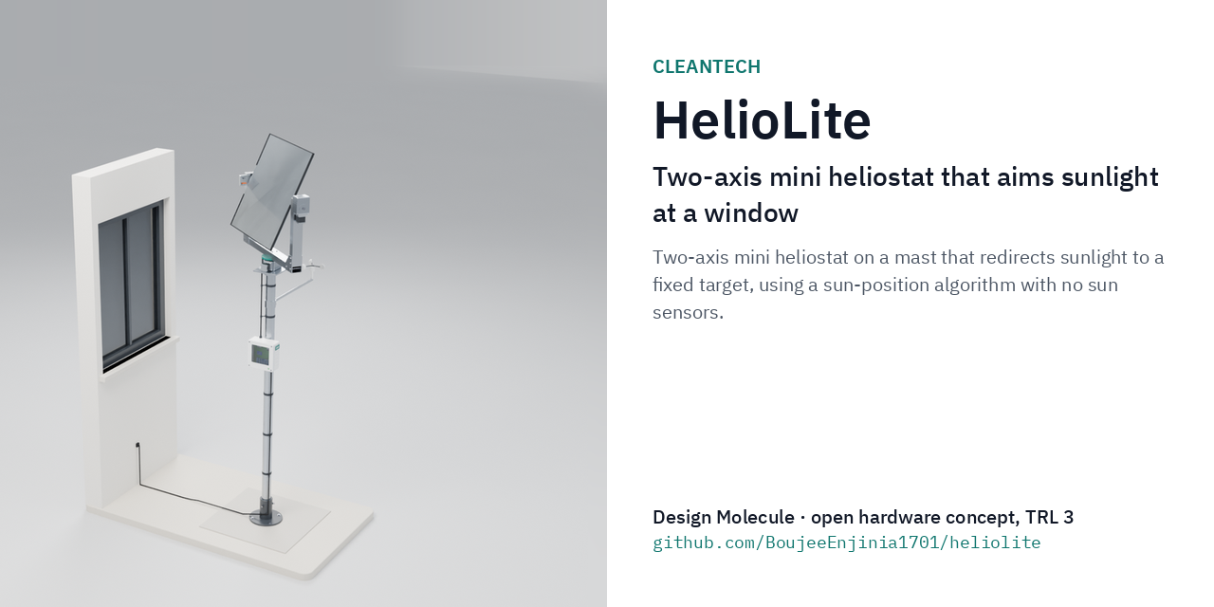
media/social-preview.png
